PeteLaric/AirHarp-Pico/documentation/song template/raw pix/0000.png

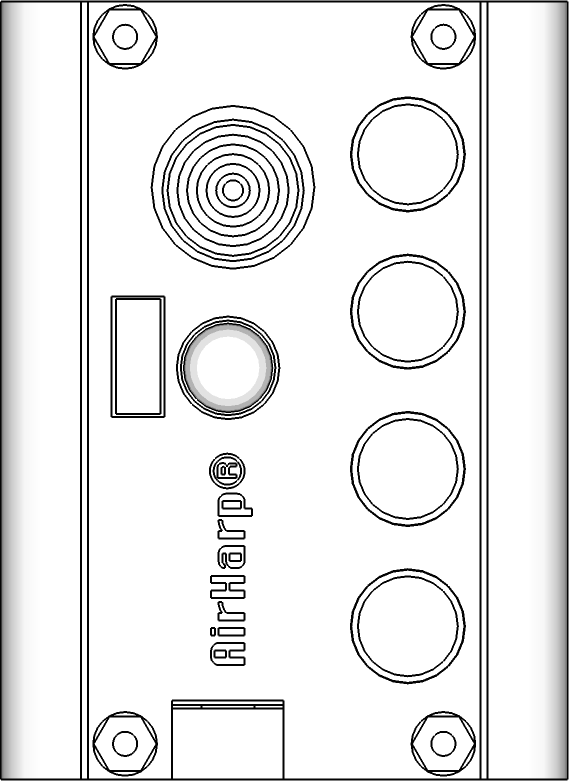
documentation/song template/raw pix/0000.png
