PeteLaric/AirHarp-Pico/documentation/song template/raw pix/0011.png

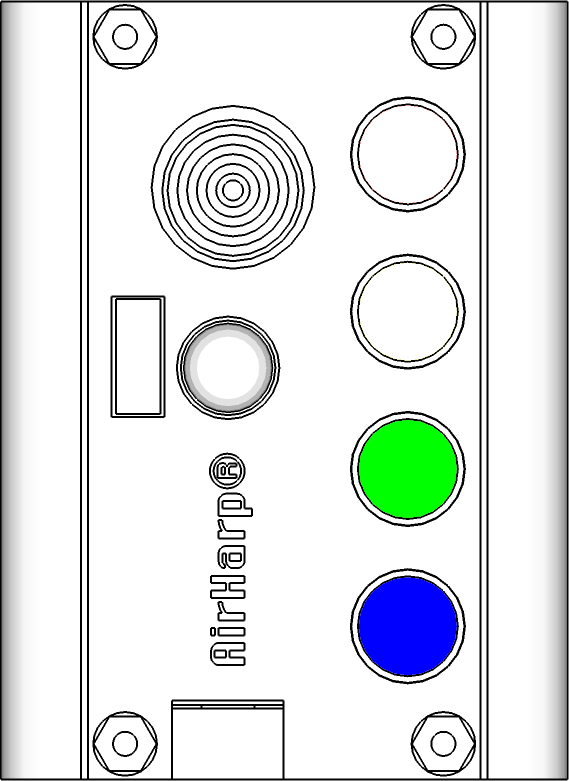
documentation/song template/raw pix/0011.png
