PeteLaric/AirHarp-Pico/documentation/song template/raw pix/0101.png

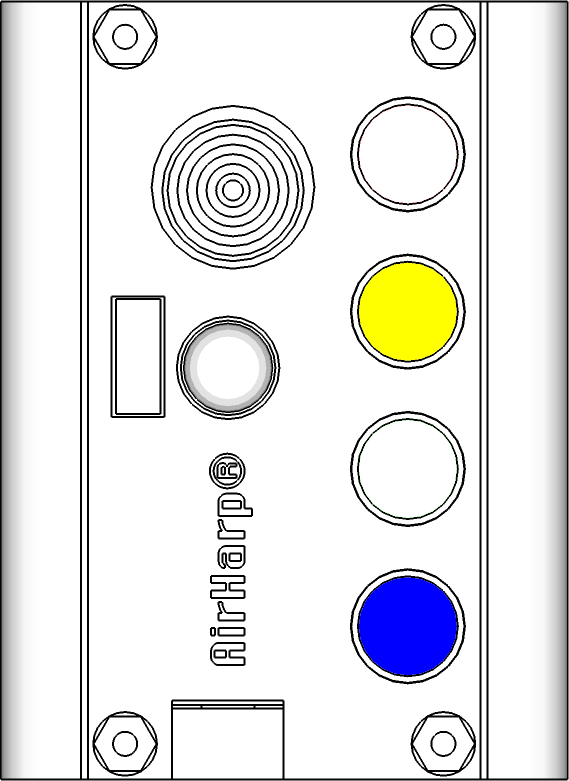
documentation/song template/raw pix/0101.png
