PeteLaric/AirHarp-Pico/documentation/song template/raw pix/0110.png

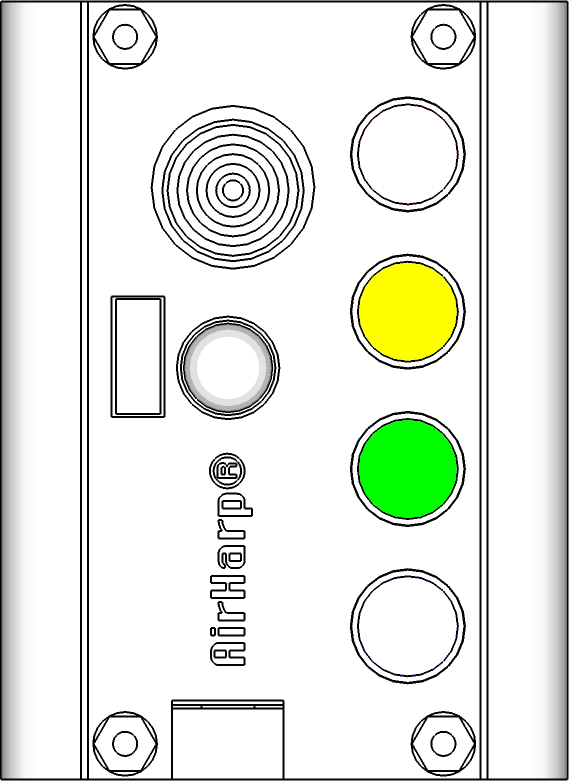
documentation/song template/raw pix/0110.png
