PeteLaric/AirHarp-Pico/documentation/song template/raw pix/1000.png

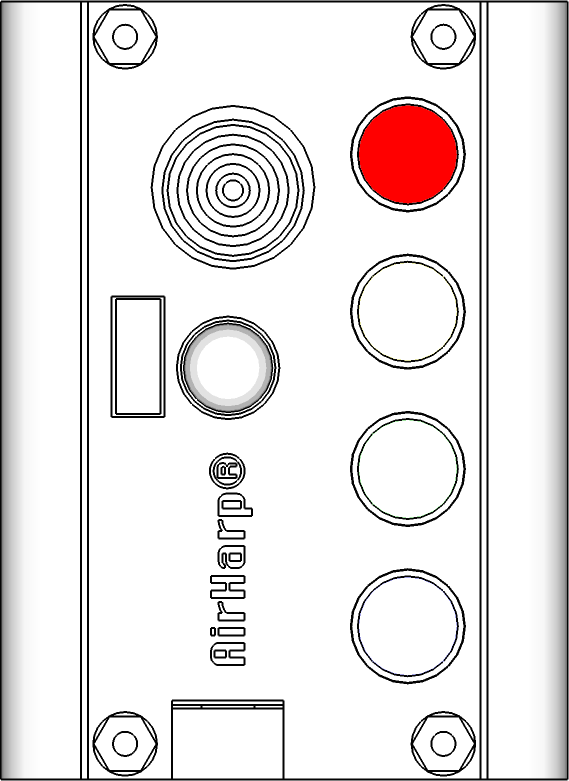
documentation/song template/raw pix/1000.png
