PeteLaric/AirHarp-Pico/documentation/song template/raw pix/1111 transpose_line.png

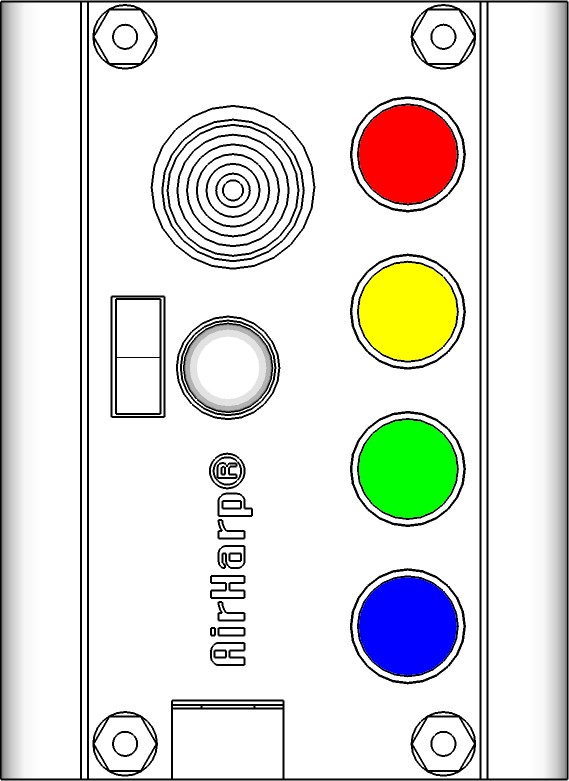
documentation/song template/raw pix/1111 transpose_line.png
