PeteLaric/AirHarp-Pico/documentation/song template/raw pix/transpose_down.png

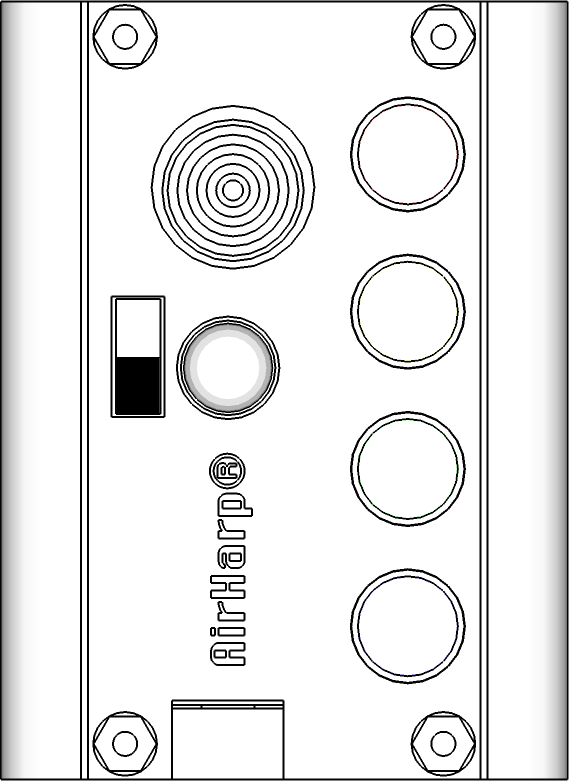
documentation/song template/raw pix/transpose_down.png
