PeteLaric/AirHarp-Pico/laser engraving/custom/Elan Noelle/Elan custom 03 65x37mm.bmp

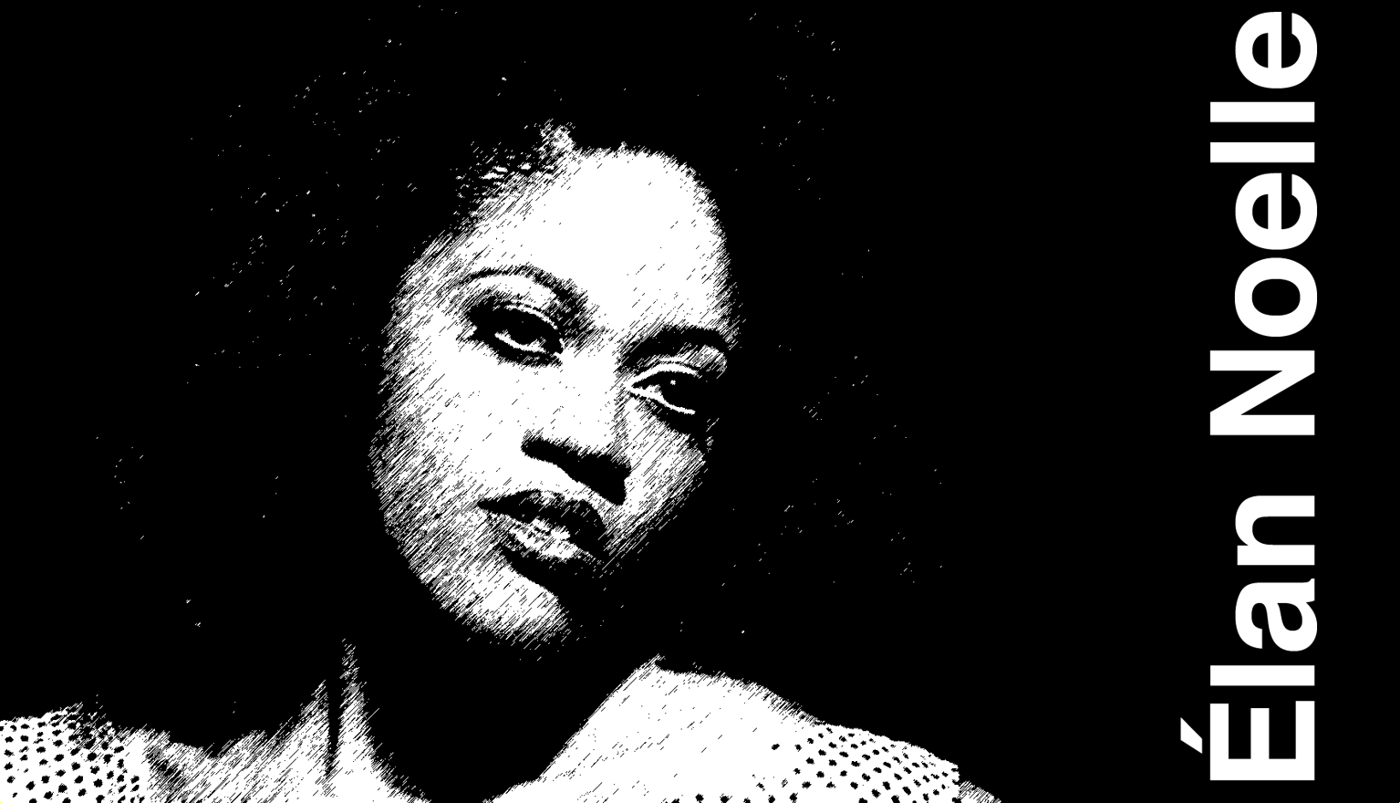
laser engraving/custom/Elan Noelle/Elan custom 03 65x37mm.bmp
