PeteLaric/AirHarp-Pico/misc/AirHarp Transposition Table 06 cropped.png

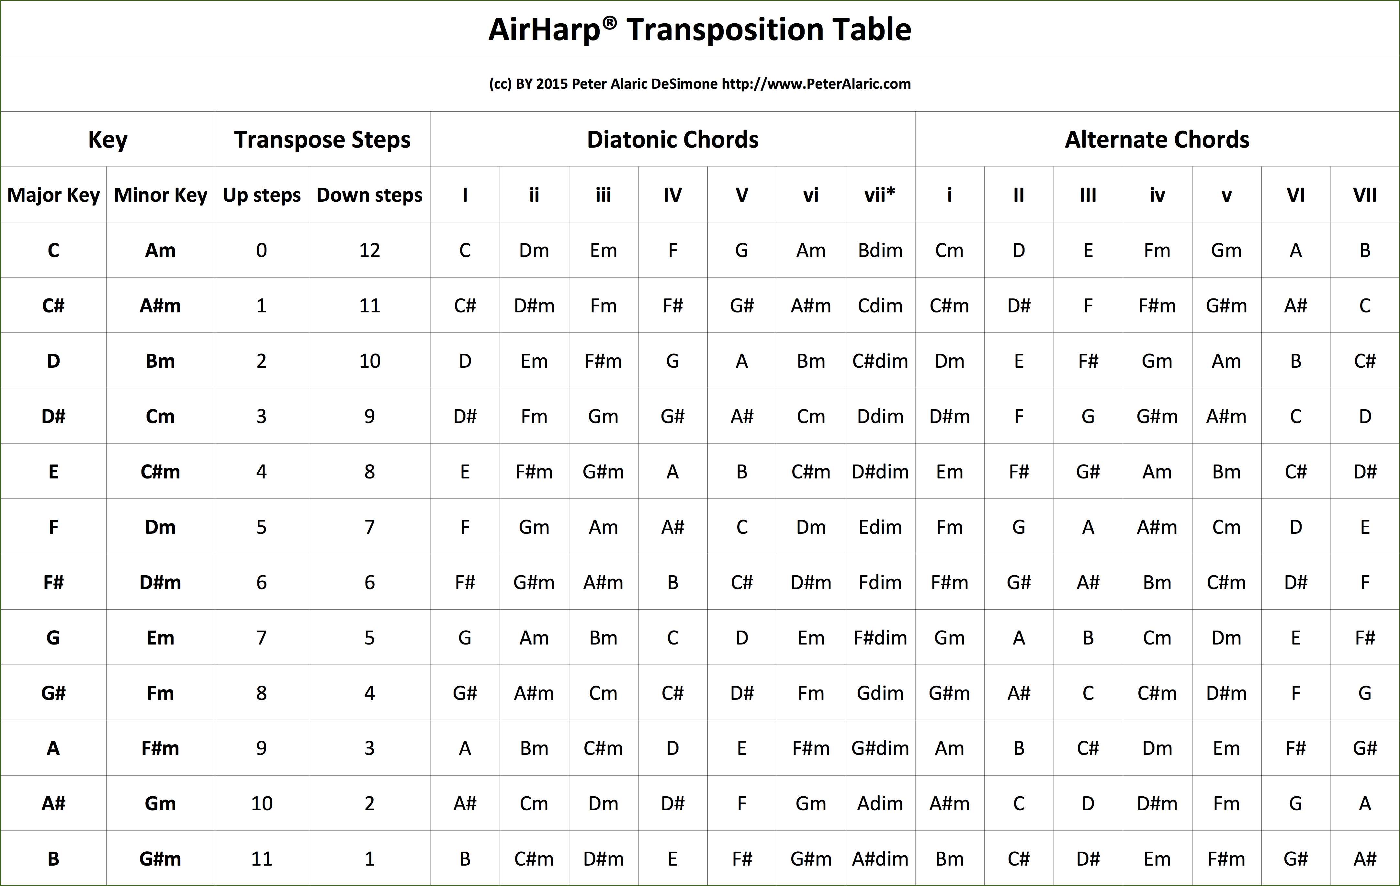
misc/AirHarp Transposition Table 06 cropped.png
