PeteLaric/AirHarp-Pico/misc/AirHarp vs Autoharp v2.png

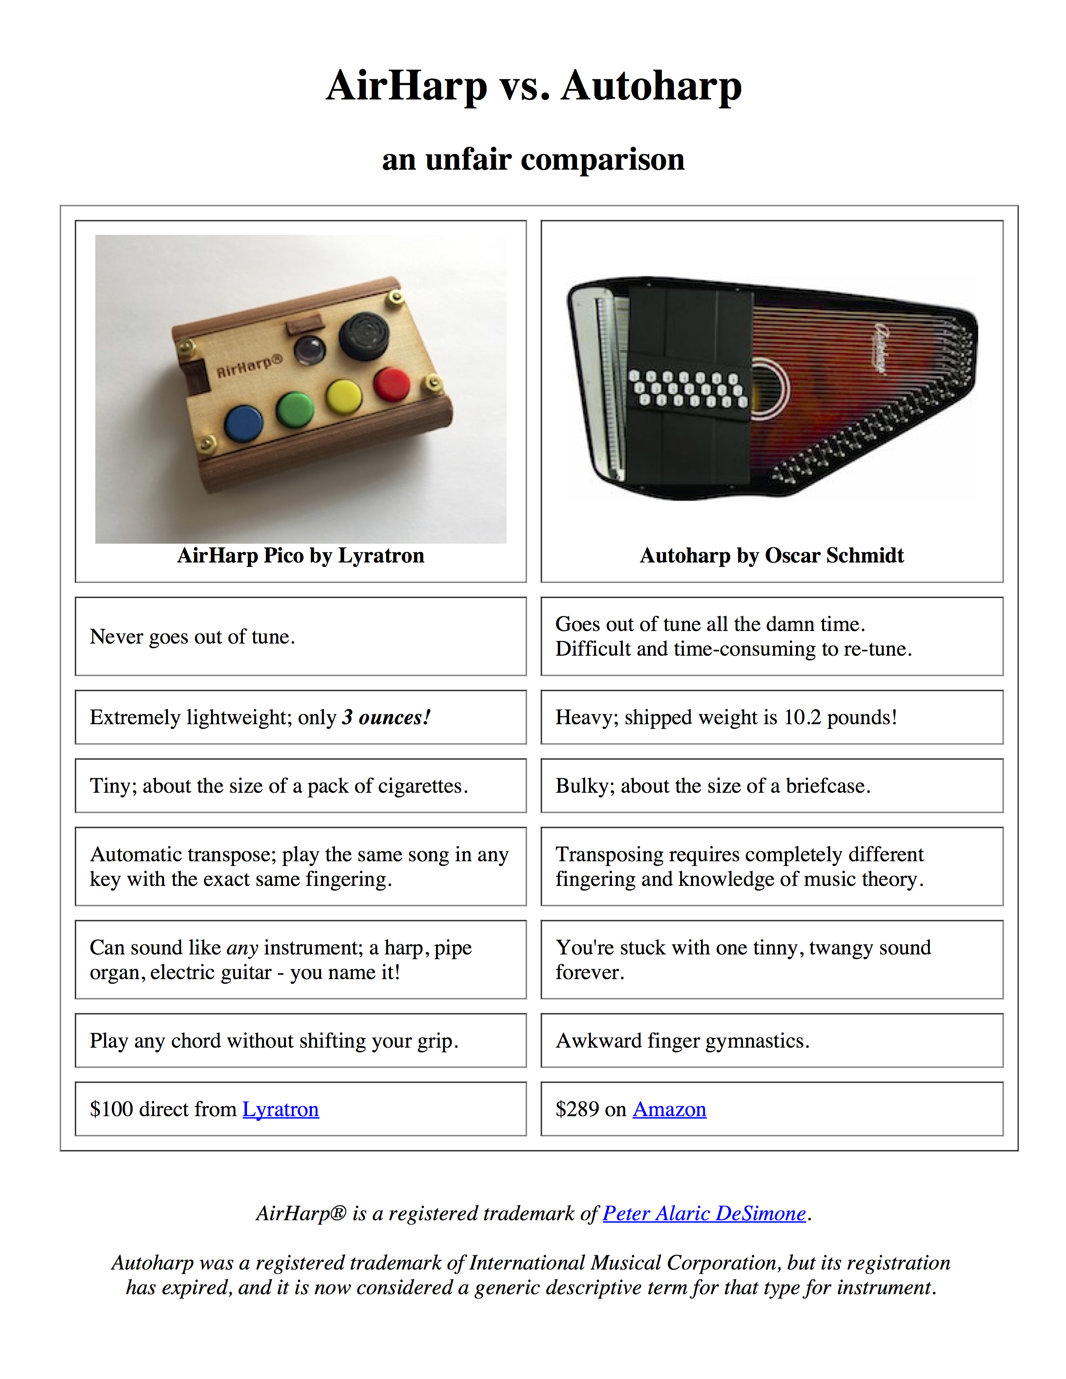
misc/AirHarp vs Autoharp v2.png
