PeteLaric/AirHarp-Pico/PCB/AirHarp Pico 1.001 no ratsnest.png

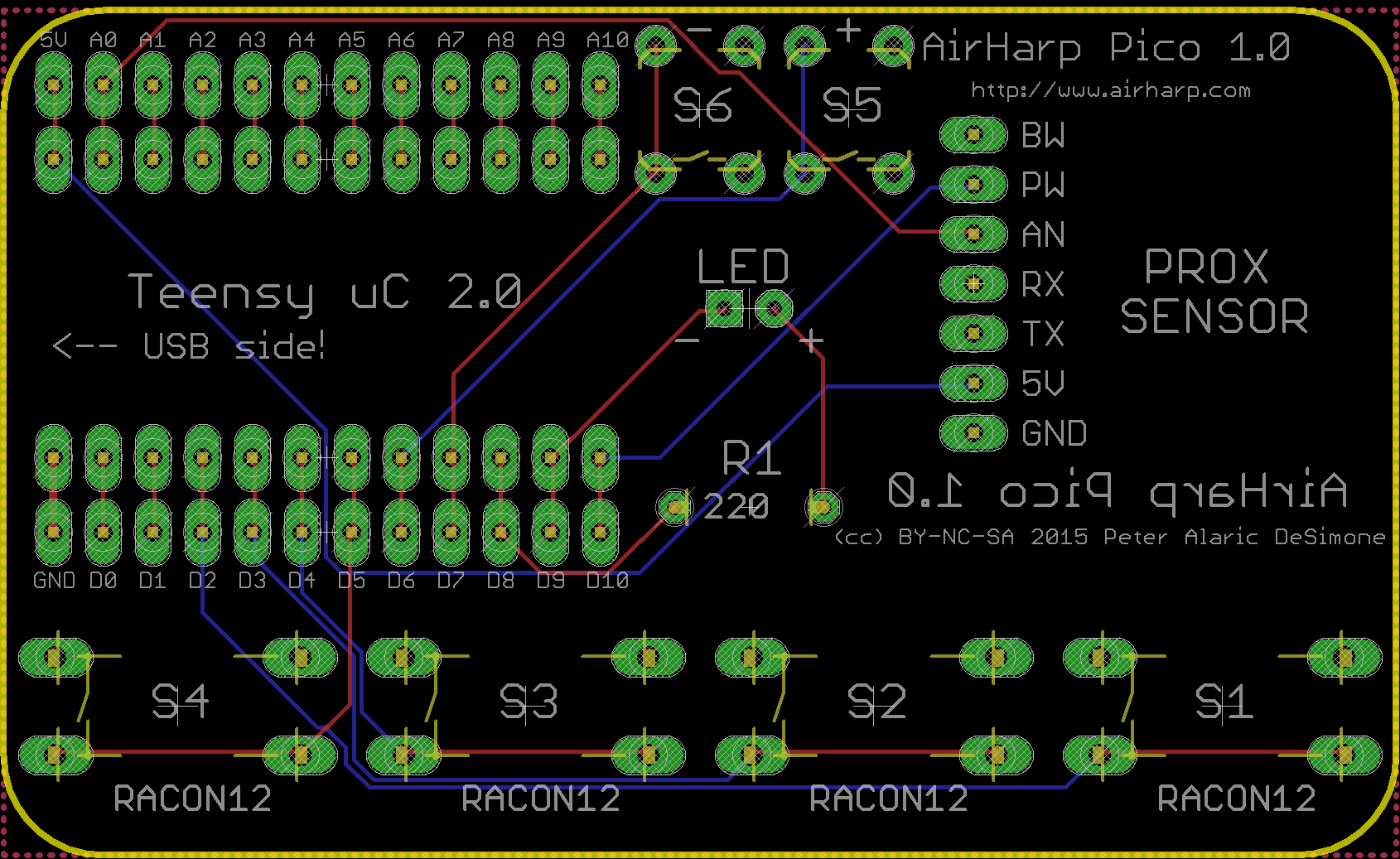
PCB/AirHarp Pico 1.001 no ratsnest.png
