PeteLaric/AirHarp-Pico/PCB/AirHarp Pico 1.001.png

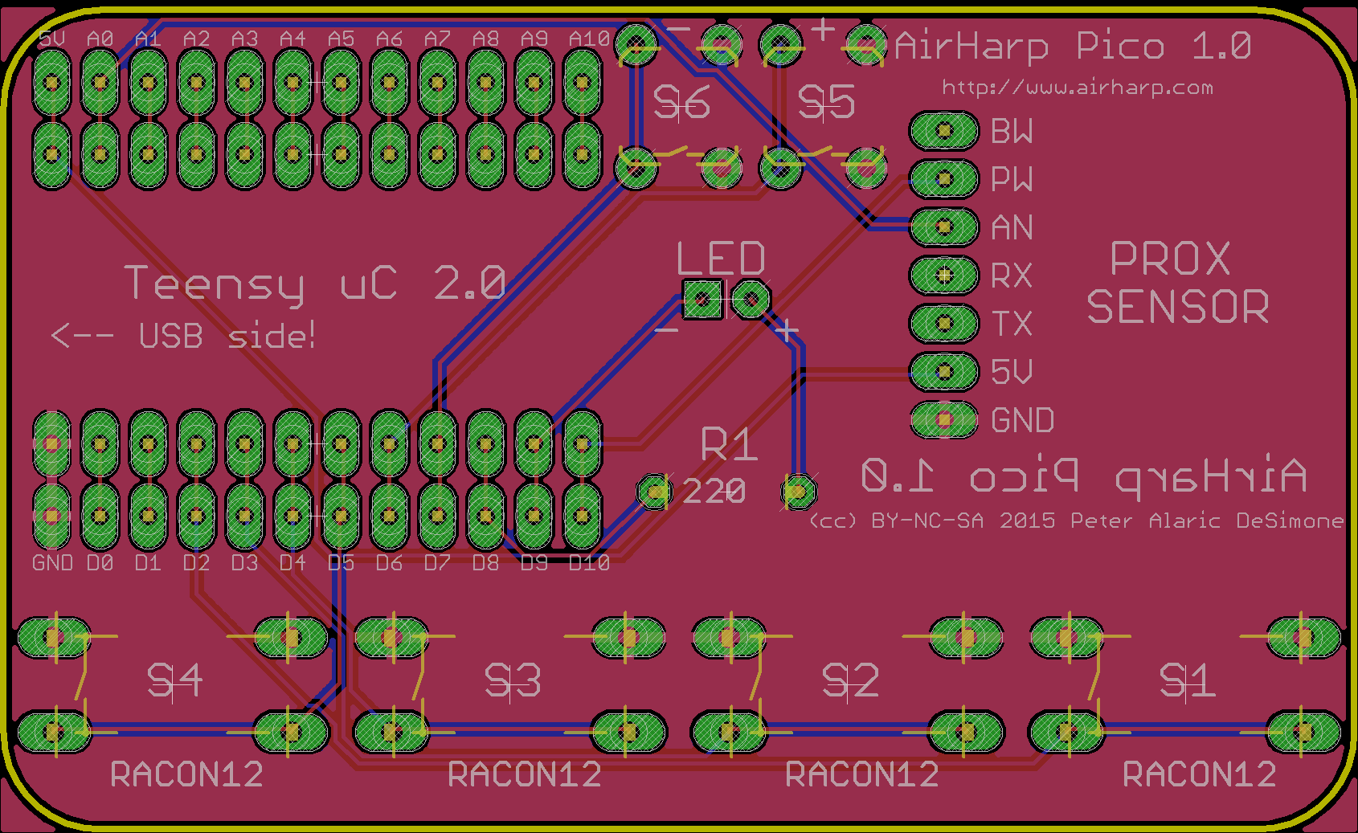
PCB/AirHarp Pico 1.001.png
