PeteLaric/AirHarp-Pico/pix/IMG_0683 back best labeled.JPG

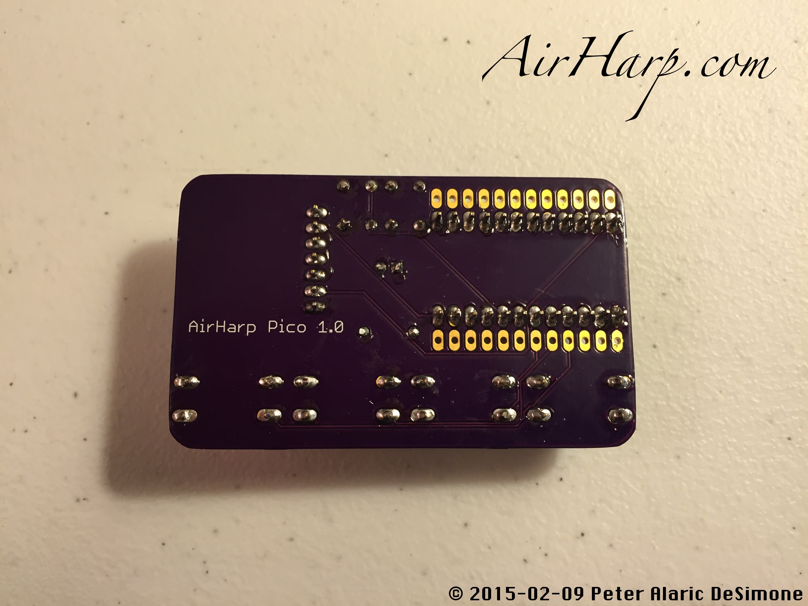
pix/IMG_0683 back best labeled.JPG
