PeteLaric/AirHarp-Pico/pix/IMG_0684 PCB best.JPG

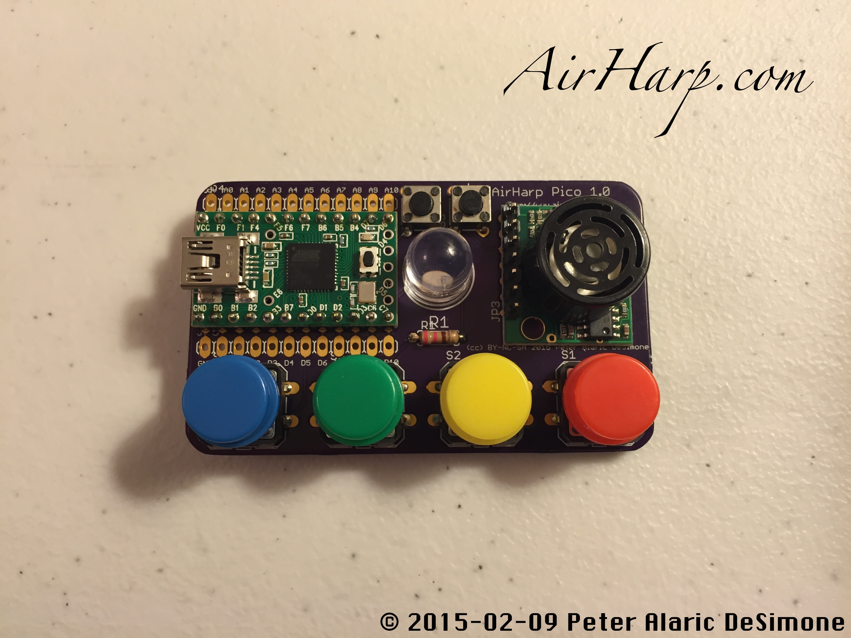
pix/IMG_0684 PCB best.JPG
