PeteLaric/AirHarp-Pico/pix/IMG_0691 with case best edit.JPG

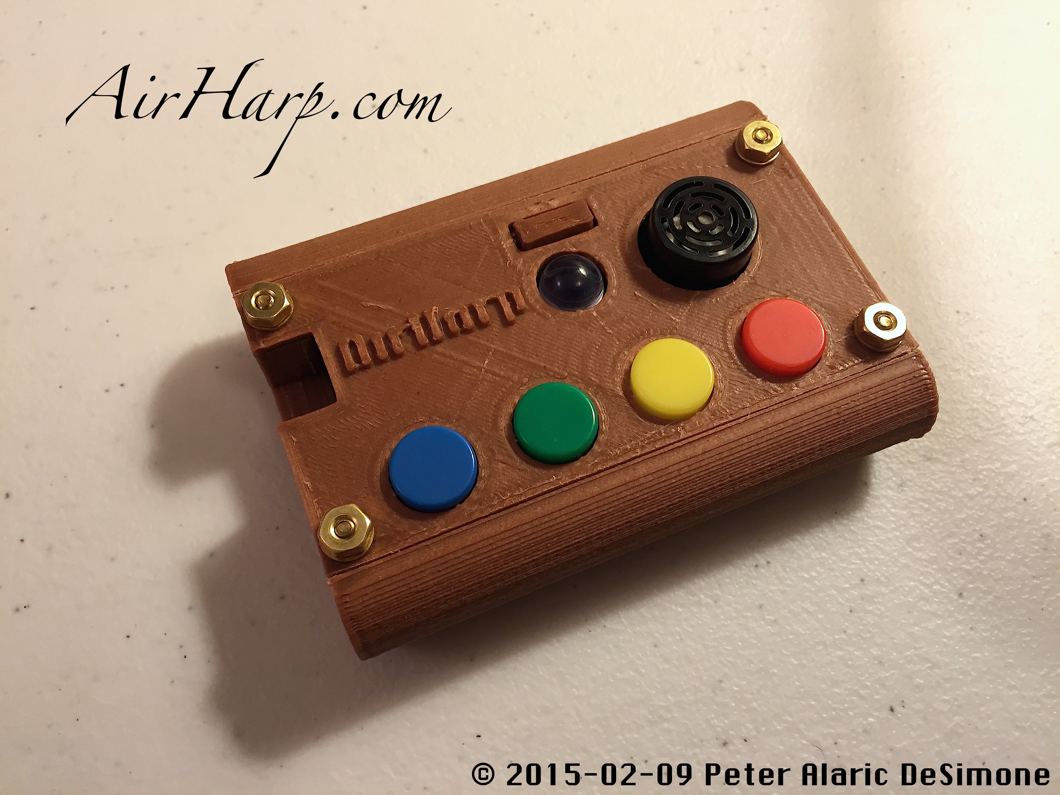
pix/IMG_0691 with case best edit.JPG
