PeteLaric/AirHarp-Pico/pix/IMG_6731 hybrid case.JPG

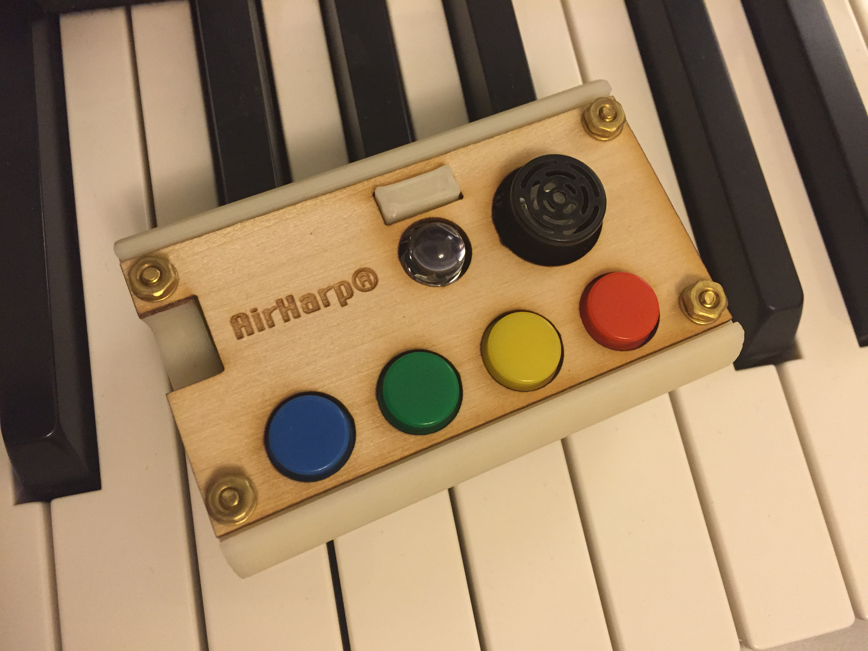
pix/IMG_6731 hybrid case.JPG
